RP-Hall/sirius/AVR/config.c

#include "config.h"


int L1 = 33;
int L2 = 60;
int L3 = 74;

//Convert to -1,-1 format
struct Gait left_rotationGait = { 10,
{
    { { { 111, 90, 90, 150 }, { 69, 90, 90, 150 }, { 112, 90, 90, 150 }, { 69, 90, 90, 150 }  } },
    { { { 31, 45, 45, 150 }, { 69, 90, 90, 150 }, { 112, 90, 90, 150 }, { 69, 90, 90, 150 }  } },
    { { { 31, 90, 90, 150 }, { 69, 90, 90, 150 }, { 112, 90, 90, 150 }, { 69, 90, 90, 150 }  } },
    { { { 31, 90, 90, 150 }, { 69, 90, 90, 150 }, { 32, 45, 45, 150 }, { 69, 90, 90, 150 } } },
    { { { 31, 90, 90, 150 }, { 69, 90, 90, 150 }, { 32, 90, 90, 150 }, { 69, 90, 90, 150 } } },
    { {	{ 111, 90, 90, 150 }, { 149, 90, 90, 150 }, { 112, 90, 90, 150 }, { 149, 90, 90, 150 } } },
    { { { 111, 90, 90, 150 }, { 69, 45, 45, 150 }, { 112, 90, 90, 150 }, { 149, 90, 90, 150 } } },
    { { { 111, 90, 90, 150 }, { 69, 90, 90, 150 }, { 112, 90, 90, 150 }, { 149, 90, 90, 150 } } },
    { { { 111, 90, 90, 150 }, { 69, 90, 90, 150 }, { 112, 90, 90, 150 }, { 69, 45, 45, 150 } } },
    { { { 111, 90, 90, 150 }, { 69, 90, 90, 150 }, { 112, 90, 90, 150 }, { 69, 90, 90, 150 } } },
} 
};

//TODO Right rotation gate

struct Gait spiderForward = {13,
{
    { { { 89, 90, 90, 150 }, { 129, 90, 90, 150 }, { 72, 90, 90, 150 }, { 149, 90, 90, 150 } } },
    { {	{ 89, 90, 90, 150 }, { 129, 90, 90, 150 }, { 72, 90, 90, 150 }, { 69, 45, 45, 150 } } },
    { { { 89, 90, 90, 150 }, { 129, 90, 90, 150 }, { 72, 90, 90, 150 }, { 69, 90, 90, 150 } } },
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
	{{{31, 60, 60, 150},{149, 60, 60, 150},{ 32, 60 , 60, 150},{149, 60, 60, 150} }},
	{{{31, 90, 90, 150},{149, 90, 90, 150},{ 32, 90 ,90, 150},{149, 90, 90, 150} }},
	{{{89, 90, 90, 150},{89, 90, 90, 150},{ 92, 90 ,90, 150},{89, 90, 90, 150} }}
}
};

struct Gait sit= {6,
{
	{{{89, 0, 0, 150},{ 89, 0, 0, 150},{ 92, 0, 0, 150},{89, 0, 0, 150} }},
	{{{31, 0, 0, 150},{149, 0, 0, 150},{ 92, 0 ,0, 150},{89, 0, 0, 150} }},
	{{{31, 40, 40, 150},{149, 40, 40, 150},{ 92, 0 , 0, 150},{89, 0, 0, 150} }},
	{{{31, 60, 60, 150},{149, 60, 60, 150},{ 92, 0 , 0, 150},{89, 0, 0, 150} }},
	{{{31, 90, 90, 150},{149, 90, 90, 150},{ 92, 0 ,0, 150},{89, 0, 0, 150} }},
	{{{89, 90, 90, 120},{89, 90, 90, 180},{ 92, 0 ,0, 150},{89, 0, 0, 150} }}
}
};

struct Gait open_transformer= {2,
{
	{{{89, 0, 0, 238},{89, 0, 0, 42},{ 92, 0 ,0, 238},{149, 0, 0, 42} }},
	{{{89, 90, 90, 150},{89, 90, 90, 150},{ 92, 0 ,0, 150},{89, 0, 0, 150} }}
}
};
