RP-Hall/sirius/AVR/lcd.c

#define F_CPU 14745600ul

#include <avr/io.h>
#include <util/delay.h>
#include <avr/interrupt.h>

#include "lcd.h"

unsigned int temp;
unsigned int unit;
unsigned int tens;
unsigned int hundred;
unsigned int thousand;
unsigned int million;

//Function to configure LCD port
void lcd_port_config ()
{
	DDRC = DDRC | 0xF7; //all the LCD pin's direction set as output
	PORTC = PORTC & 0x80; // all the LCD pins are set to logic 0 except PORTC 7
}



//Function to Reset LCD
void lcd_set_4bit()
{
	_delay_ms(1);

	cbit(lcd_port,RS);				//RS=0 --- Command Input
	cbit(lcd_port,RW);				//RW=0 --- Writing to LCD
	lcd_port = 0x30;				//Sending 3
	sbit(lcd_port,EN);				//Set Enable Pin
	_delay_ms(5);					//Delay
	cbit(lcd_port,EN);				//Clear Enable Pin

	_delay_ms(1);

	cbit(lcd_port,RS);				//RS=0 --- Command Input
	cbit(lcd_port,RW);				//RW=0 --- Writing to LCD
	lcd_port = 0x30;				//Sending 3
	sbit(lcd_port,EN);				//Set Enable Pin
	_delay_ms(5);					//Delay
	cbit(lcd_port,EN);				//Clear Enable Pin

	_delay_ms(1);

	cbit(lcd_port,RS);				//RS=0 --- Command Input
	cbit(lcd_port,RW);				//RW=0 --- Writing to LCD
	lcd_port = 0x30;				//Sending 3
	sbit(lcd_port,EN);				//Set Enable Pin
	_delay_ms(5);					//Delay
	cbit(lcd_port,EN);				//Clear Enable Pin

	_delay_ms(1);

	cbit(lcd_port,RS);				//RS=0 --- Command Input
	cbit(lcd_port,RW);				//RW=0 --- Writing to LCD
	lcd_port = 0x20;				//Sending 2 to initialise LCD 4-bit mode
	sbit(lcd_port,EN);				//Set Enable Pin
	_delay_ms(5);					//Delay
	cbit(lcd_port,EN);				//Clear Enable Pin

	
}

//Function to Initialize LCD
void lcd_init()
{
	lcd_port_config();
	lcd_set_4bit();
	_delay_ms(1);
	lcd_wr_command(0x28);			//LCD 4-bit mode and 2 lines.
	lcd_wr_command(0x01);
	lcd_wr_command(0x06);
	lcd_wr_command(0x0E);
	lcd_wr_command(0x80);
}


//Function to Write Command on LCD
void lcd_wr_command(unsigned char cmd)
{
	unsigned char temp;
	temp = cmd;
	temp = temp & 0xF0;
	lcd_port &= 0x0F;
	lcd_port |= temp;
	cbit(lcd_port,RS);
	cbit(lcd_port,RW);
	sbit(lcd_port,EN);
	_delay_ms(5);
	cbit(lcd_port,EN);
	
	cmd = cmd & 0x0F;
	cmd = cmd<<4;
	lcd_port &= 0x0F;
	lcd_port |= cmd;
	cbit(lcd_port,RS);
	cbit(lcd_port,RW);
	sbit(lcd_port,EN);
	_delay_ms(5);
	cbit(lcd_port,EN);
}

//Function to Write Data on LCD
void lcd_wr_char(char letter)
{
	char temp;
	temp = letter;
	temp = (temp & 0xF0);
	lcd_port &= 0x0F;
	lcd_port |= temp;
	sbit(lcd_port,RS);
	cbit(lcd_port,RW);
	sbit(lcd_port,EN);
	_delay_ms(5);
	cbit(lcd_port,EN);

	letter = letter & 0x0F;
	letter = letter<<4;
	lcd_port &= 0x0F;
	lcd_port |= letter;
	sbit(lcd_port,RS);
	cbit(lcd_port,RW);
	sbit(lcd_port,EN);
	_delay_ms(5);
	cbit(lcd_port,EN);
}


//Function to bring cursor at home position
void lcd_home()
{
	lcd_wr_command(0x80);
}


//Function to Print String on LCD
void lcd_string(char *str)
{
	while(*str != '\0')
	{
		lcd_wr_char(*str);
		str++;
	}
}

//Position the LCD cursor at "row", "column".

void lcd_cursor (char row, char column)
{
	switch (row) {
		case 1: lcd_wr_command (0x80 + column - 1); break;
		case 2: lcd_wr_command (0xc0 + column - 1); break;
		case 3: lcd_wr_command (0x94 + column - 1); break;
		case 4: lcd_wr_command (0xd4 + column - 1); break;
		default: break;
	}
}

//Function To Print Any input value upto the desired digit on LCD
void lcd_print (char row, char coloumn, unsigned int value, int digits)
{
	unsigned char flag=0;
	if(row==0||coloumn==0)
	{
		lcd_home();
	}
	else
	{
		lcd_cursor(row,coloumn);
	}
	if(digits==5 || flag==1)
	{
		million=value/10000+48;
		lcd_wr_char(million);
		flag=1;
	}
	if(digits==4 || flag==1)
	{
		temp = value/1000;
		thousand = temp%10 + 48;
		lcd_wr_char(thousand);
		flag=1;
	}
	if(digits==3 || flag==1)
	{
		temp = value/100;
		hundred = temp%10 + 48;
		lcd_wr_char(hundred);
		flag=1;
	}
	if(digits==2 || flag==1)
	{
		temp = value/10;
		tens = temp%10 + 48;
		lcd_wr_char(tens);
		flag=1;
	}
	if(digits==1 || flag==1)
	{
		unit = value%10 + 48;
		lcd_wr_char(unit);
	}
	if(digits>5)
	{
		lcd_wr_char('E');
	}
	
}


void display_clear(void)
{
	lcd_wr_command(0x01);
}

void print_hex(char ch)
{
	char nibbleh = (ch & 0xF0)>>4;
	char nibblel = (ch & 0x0F);
	
	switch(nibbleh)
	{
		case 0: lcd_wr_char('0');break;
		case 1: lcd_wr_char('1');break;
		case 2: lcd_wr_char('2');break;
		case 3: lcd_wr_char('3');break;
		case 4: lcd_wr_char('4');break;
		case 5: lcd_wr_char('5');break;
		case 6: lcd_wr_char('6');break;
		case 7: lcd_wr_char('7');break;
		case 8: lcd_wr_char('8');break;
		case 9: lcd_wr_char('9');break;
		case 10: lcd_wr_char('A');break;
		case 11: lcd_wr_char('B');break;
		case 12: lcd_wr_char('C');break;
		case 13: lcd_wr_char('D');break;
		case 14: lcd_wr_char('E');break;
		case 15: lcd_wr_char('F');break;
		default:break;
	}		
	
	switch(nibblel)
	{
		case 0: lcd_wr_char('0');break;
		case 1: lcd_wr_char('1');break;
		case 2: lcd_wr_char('2');break;
		case 3: lcd_wr_char('3');break;
		case 4: lcd_wr_char('4');break;
		case 5: lcd_wr_char('5');break;
		case 6: lcd_wr_char('6');break;
		case 7: lcd_wr_char('7');break;
		case 8: lcd_wr_char('8');break;
		case 9: lcd_wr_char('9');break;
		case 10: lcd_wr_char('A');break;
		case 11: lcd_wr_char('B');break;
		case 12: lcd_wr_char('C');break;
		case 13: lcd_wr_char('D');break;
		case 14: lcd_wr_char('E');break;
		case 15: lcd_wr_char('F');break;
		default:break;
	}
}
